UMS-Ultra/BubbleBox/Images/BubbleBox Black and Light Grey Square Truncated Keycaps.jpg

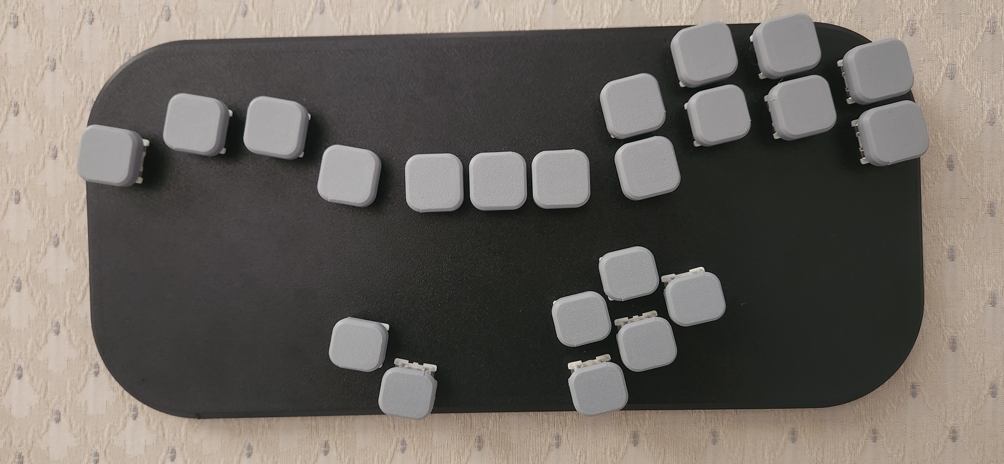
Images/BubbleBox Black and Light Grey Square Truncated Keycaps.jpg
