UMS-Ultra/BubbleBox/Images/BubbleBox Light Grey and Purple Hex Keycaps.jpg

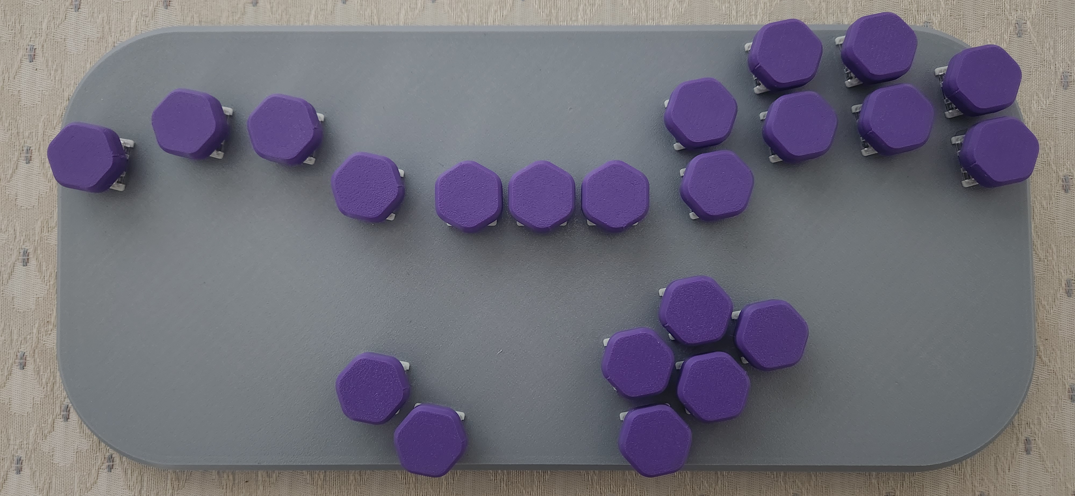
Images/BubbleBox Light Grey and Purple Hex Keycaps.jpg
