UMS-Ultra/BubbleBox/Images/Model BirdD Transparentish.png

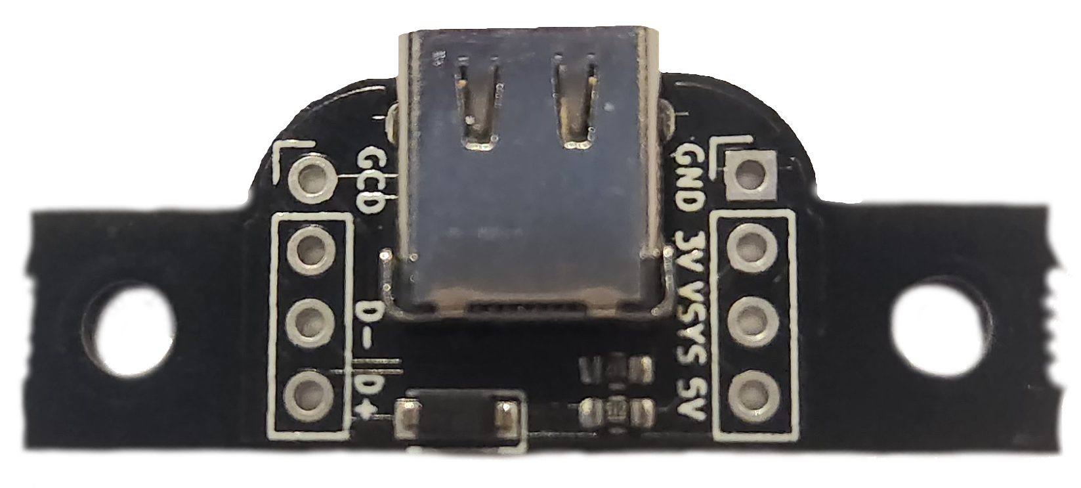
Images/Model BirdD Transparentish.png
