UMS-Ultra/BubbleBox/Images/Model BirdD.jpg

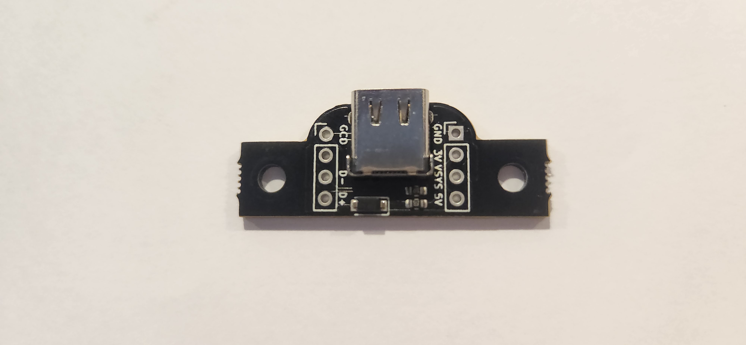
Images/Model BirdD.jpg
