UMS-Ultra/BubbleBox/Images/Pico Underside.jpg

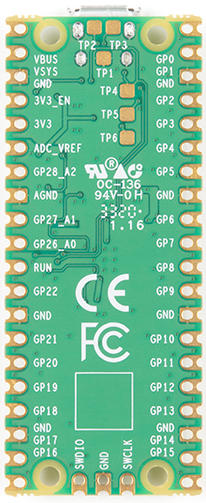
Images/Pico Underside.jpg
