UMS-Ultra/BubbleBox/Images/Split Case M3 Screw Locations Left.jpg

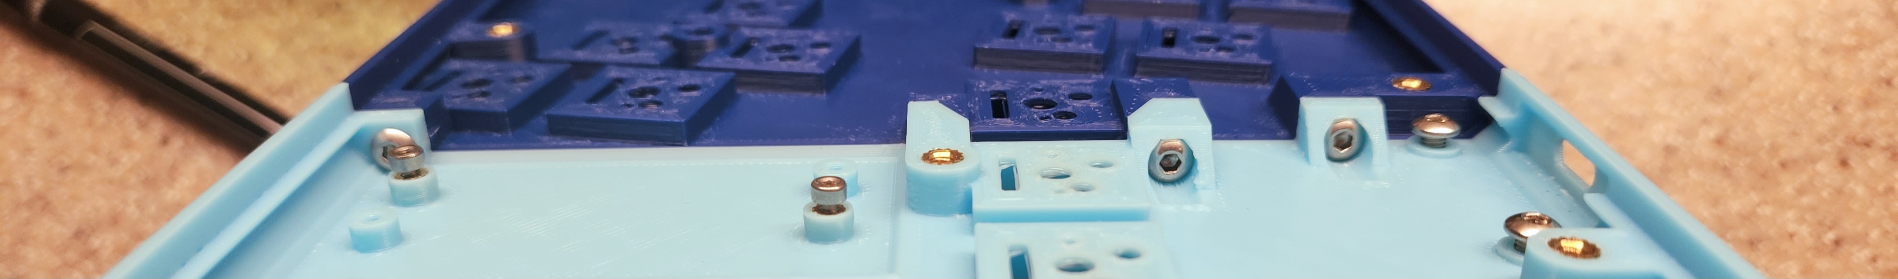
Images/Split Case M3 Screw Locations Left.jpg
