UMS-Ultra/BubbleBox/Images/Split Case M3 Screw Locations Right.jpg

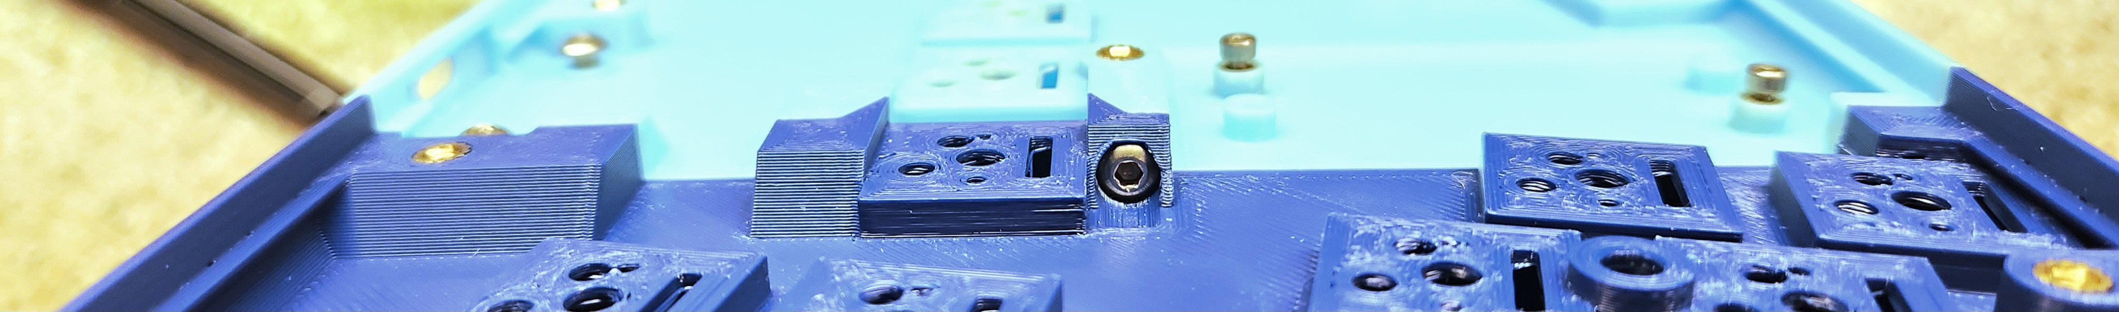
Images/Split Case M3 Screw Locations Right.jpg
