UMS-Ultra/BubbleBox/Controller Body Print Files/Split Case Files/BubbleBox V4 SCR LH Standard.STEP

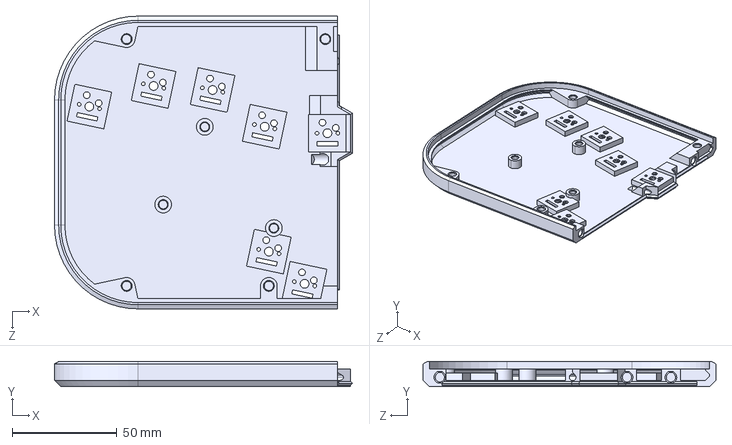
[picture p66: CAD file, 2023-04-26]
Controller Body Print Files/Split Case Files/BubbleBox V4 SCR LH Standard.STEP
142.5 x 12.0 x 140.0 mm
