UMS-Ultra/BubbleBox/Keycap Print Files/Button V4 Sq Tr 19x17mm.STEP

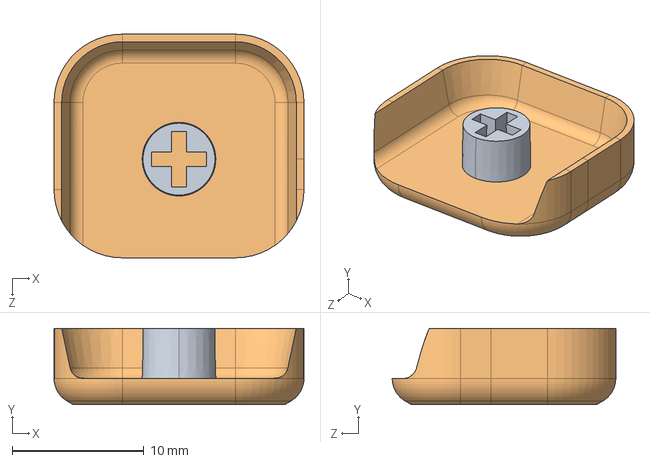
[picture p67: CAD file, 2022-10-16]
Keycap Print Files/Button V4 Sq Tr 19x17mm.STEP
19.0 x 5.80 x 17.0 mm
