UMS-Ultra/BubbleBox/Keycap Print Files/Low Profile Keycaps/Button LP V1 Hex 20mm.STEP

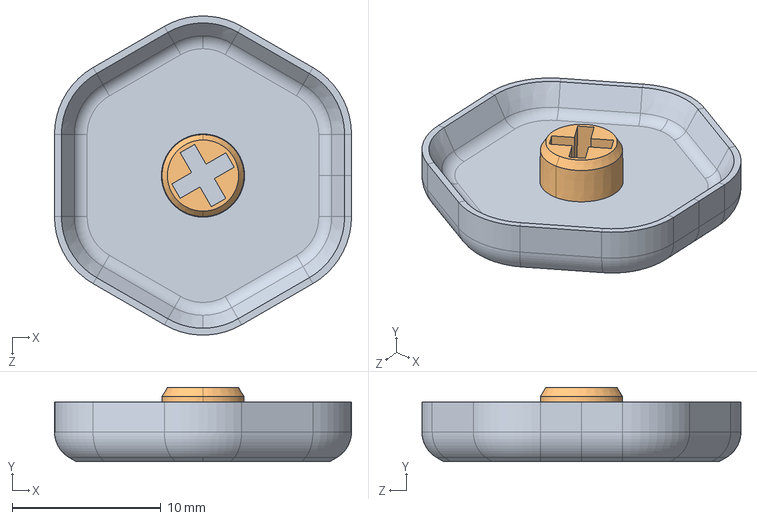
[picture p68: CAD file, 2022-10-16]
Keycap Print Files/Low Profile Keycaps/Button LP V1 Hex 20mm.STEP
20.0 x 5.00 x 21.5 mm
