UMS-Ultra/BubbleBox/Controller Body Print Files/Split Case Files/BubbleBox V4 SCL RH WASD.STEP

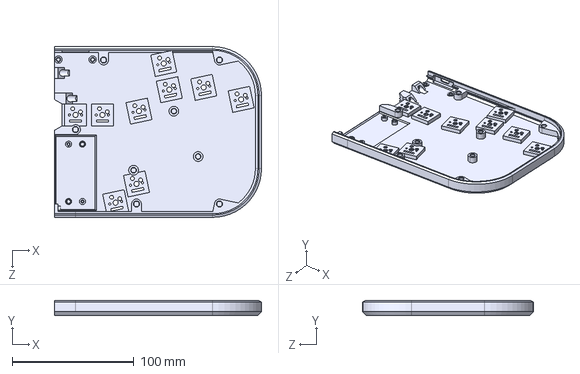
[picture p70: CAD file, 2023-04-26]
Controller Body Print Files/Split Case Files/BubbleBox V4 SCL RH WASD.STEP
169.8 x 12.0 x 140.0 mm
