UMS-Ultra/BubbleBox/Controller Body Print Files/Split Case Files/BubbleBox V4 SCR RH Standard.STEP

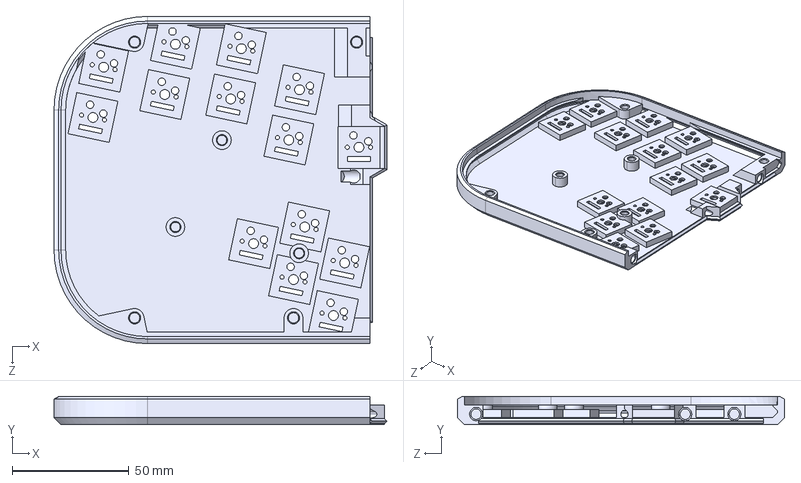
[picture p71: CAD file, 2023-04-26]
Controller Body Print Files/Split Case Files/BubbleBox V4 SCR RH Standard.STEP
142.5 x 12.0 x 140.0 mm
